Vikr-182/Indoor-Air-Quality/docs/imgs/2_pcb.png

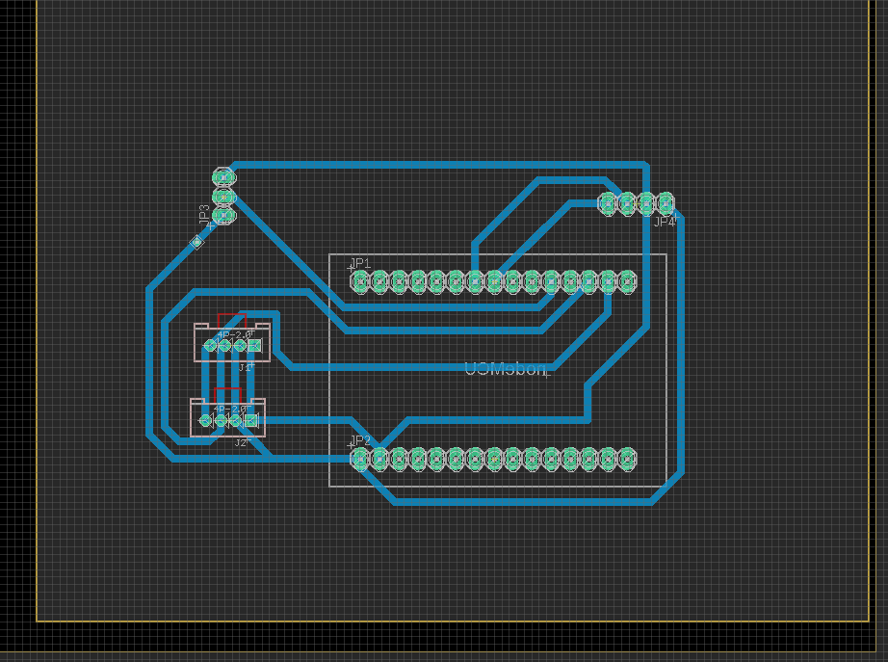
docs/imgs/2_pcb.png
