Vikr-182/Indoor-Air-Quality/docs/imgs/PM2.5 and PM10.png

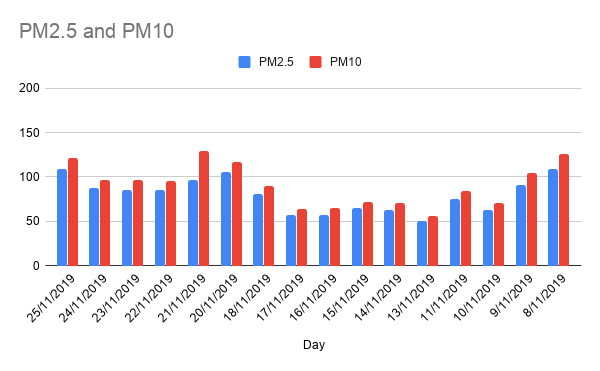
docs/imgs/PM2.5 and PM10.png
