Vikr-182/Indoor-Air-Quality/tweet/imgs/afternoon.jpeg

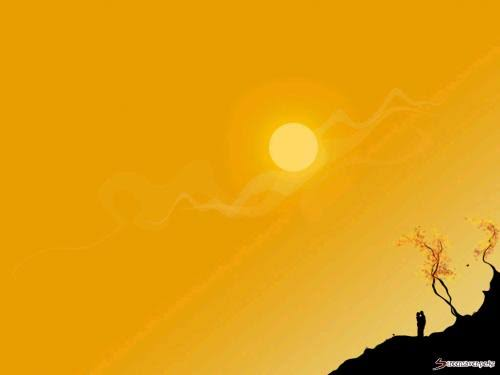
tweet/imgs/afternoon.jpeg
