Vikr-182/Indoor-Air-Quality/tweet/imgs/dusk.jpeg

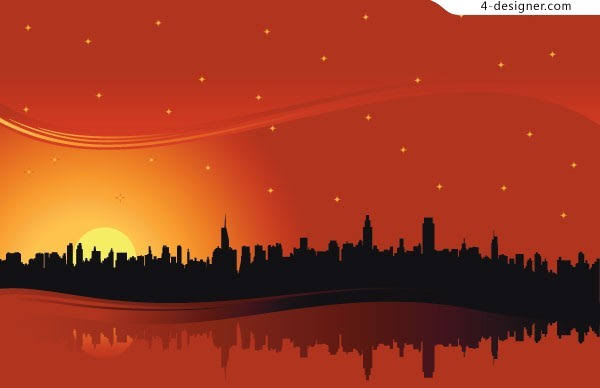
tweet/imgs/dusk.jpeg
