Vikr-182/Indoor-Air-Quality/tweet/imgs/foo.png

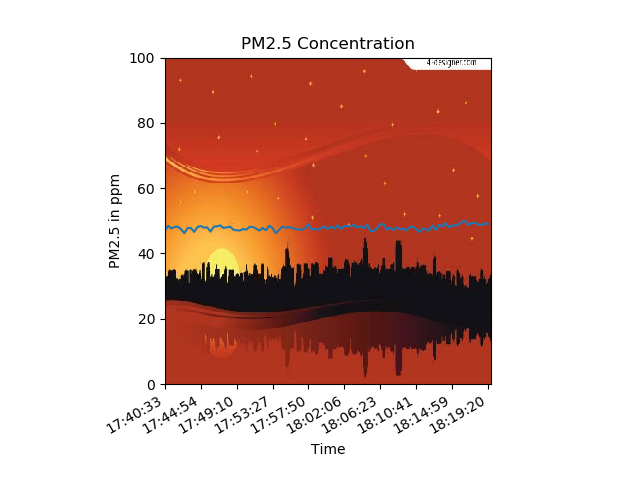
tweet/imgs/foo.png
