Vikr-182/Indoor-Air-Quality/docs/imgs/printing.jpg

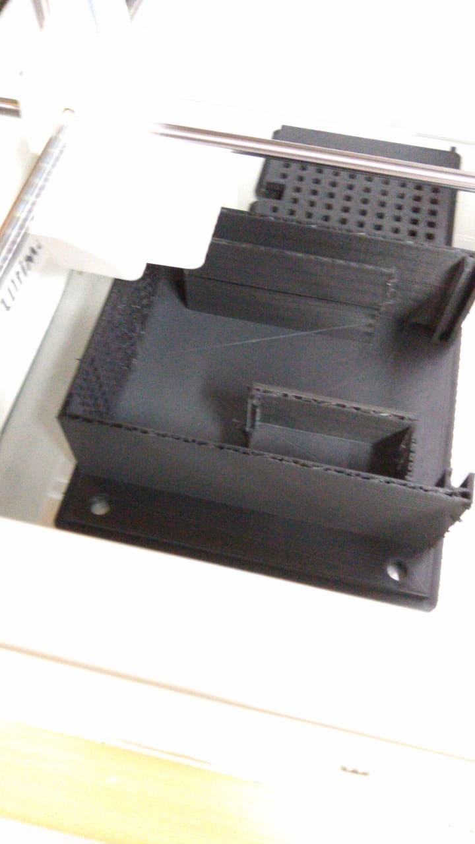
docs/imgs/printing.jpg
